tr14ngle/bcg-pid/bcg_spice/output_lvlshift.png

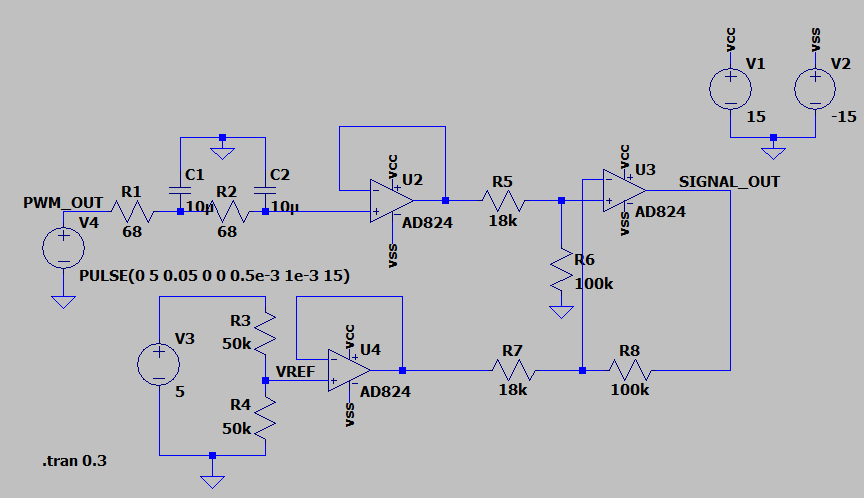
bcg_spice/output_lvlshift.png
