tr14ngle/bcg-pid/bcg_spice/lvl_shifter.asc

R1: res; 100k
R2: res; 100k
R3: res; 15k
R4: res; 100k
R5: res; 15k
U1: AD824
V1: voltage; 2.5
V2: voltage; 5
V4: voltage; SINE(0 15 200 0 0 0 50)
Named nets: 0, 2.5V, 5V, OUT, IN
.tran 0.3
