tr14ngle/bcg-pid/bcg_spice/pid2_2.asc

C1: cap; 1µ
CD: cap; 0.1µ
CI: cap; 1µ
E1: e; 100
E2: e; -0.01
L1: ind; 250
R1: res; 10k
R2: res; 10k
R4: res; 10k
R5: res; 10k
R6: res; 10k
R7: res; 10k
R8: res; 10k
R9: res; 10k
R10: res; 10k
R11: res; 10k
RC: res; 200
RD: res; 1K
RI: res; 100Meg
RP1: res; 1k
RP2: res; 2k
U1: UniversalOpAmp
U2: UniversalOpAmp
U3: UniversalOpAmp
U4: UniversalOpAmp
U5: UniversalOpAmp
U6: UniversalOpAmp
V1: voltage; 15
V2: voltage; -15
vset: voltage; PULSE(0 1 0.3 0 0 0.5 4 1)
Named nets: 0, Vcc, Vee, pid_out, pid_in, v_out
.tran 10
