tr14ngle/bcg-pid/bcg_spice/output_lvlshift.asc

C1: cap; 10µ
C2: cap; 10µ
R1: res; 68
R2: res; 68
R3: res; 50k
R4: res; 50k
R5: res; 18k
R6: res; 100k
R7: res; 18k
R8: res; 100k
U2: AD824
U3: AD824
U4: AD824
V1: voltage; 15
V2: voltage; -15
V3: voltage; 5
V4: voltage; PULSE(0 5 0.05 0 0 9e-4 1e-3 15)
Named nets: 0, vcc, vss
.tran 0.3
